KaiserSoft/OpenSimButtonBox/Cases and Enclosures/140mm wide/STL/Main Module - Face Plate - v4 - NO HOLES.STL

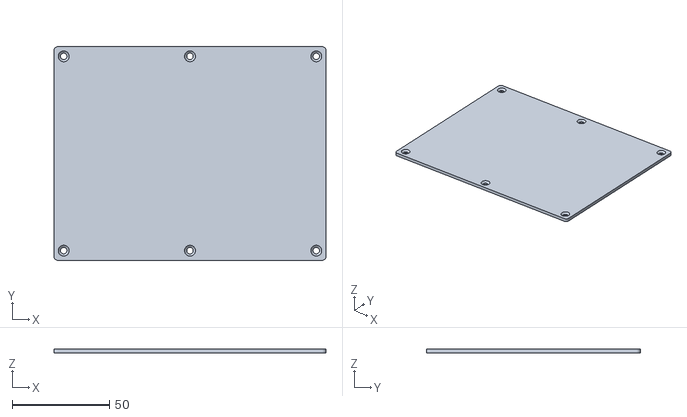
[picture p8: CAD file, 2016-06-05]
Cases and Enclosures/140mm wide/STL/Main Module - Face Plate - v4 - NO HOLES.STL
140.0 x 110.0 x 2.00
