KaiserSoft/OpenSimButtonBox/Cases and Enclosures/Mounting Bracket/Lowered Bracket/Mount Bracket 75 degrees.STL

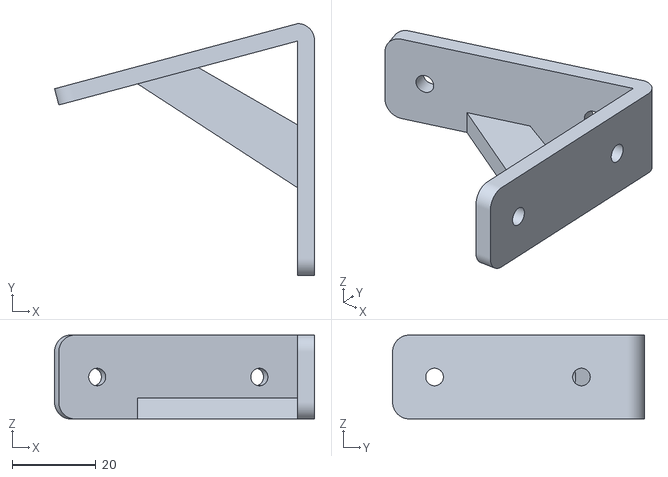
[picture p9: CAD file, 2016-05-30]
Cases and Enclosures/Mounting Bracket/Lowered Bracket/Mount Bracket 75 degrees.STL
62.0 x 60.0 x 20.0
