KaiserSoft/OpenSimButtonBox/Cases and Enclosures/Side Box Left/STL/Side Box Left - Face Plate v2 - TOP ROW PUSH BUTTONS.STL

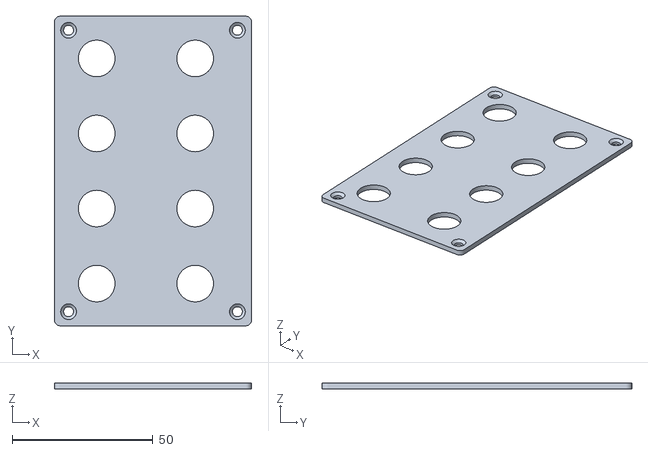
[picture p10: CAD file, 2016-12-20]
Cases and Enclosures/Side Box Left/STL/Side Box Left - Face Plate v2 - TOP ROW PUSH BUTTONS.STL
70.0 x 110.0 x 2.00
