KaiserSoft/OpenSimButtonBox/Magnetic Paddle Shifters/Box Style/Box Style - Body Top - RC1.STEP

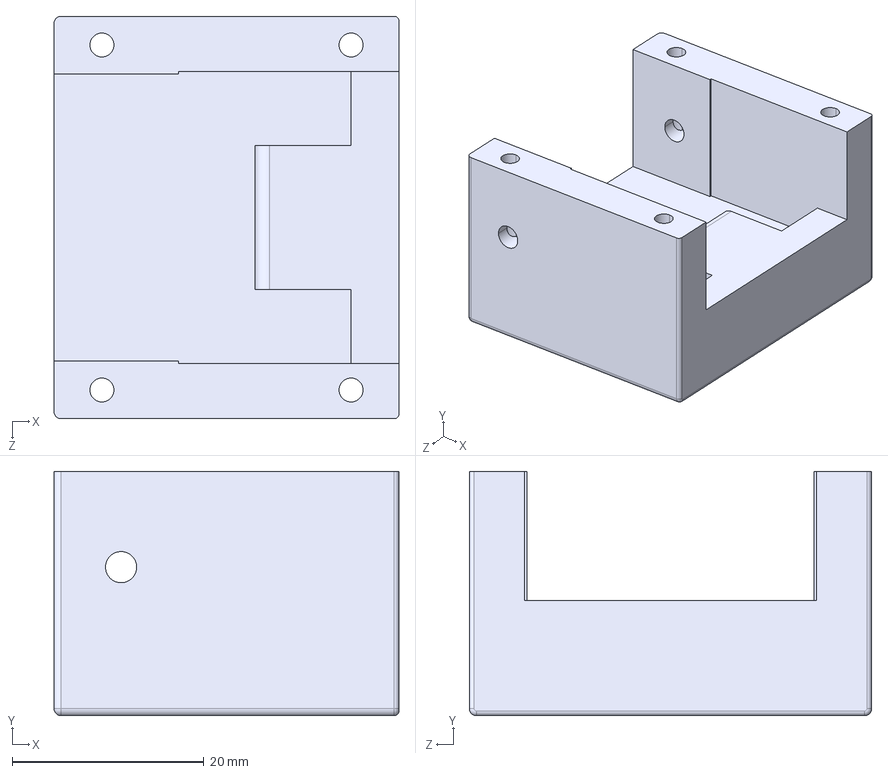
[picture p11: CAD file, 2017-08-28]
Magnetic Paddle Shifters/Box Style/Box Style - Body Top - RC1.STEP
36.0 x 25.5 x 42.0 mm
