KaiserSoft/OpenSimButtonBox/Wheel Button Box/Face Plate for 320mm Steering Wheel/Sparko - Momo - Spacer and Backplate - ProMicro.STEP

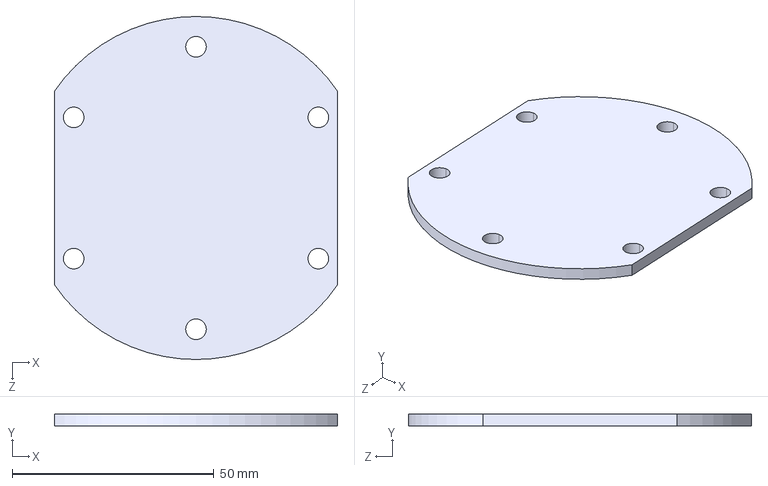
[picture p12: CAD file, 2017-09-29]
Wheel Button Box/Face Plate for 320mm Steering Wheel/Sparko - Momo - Spacer and Backplate - ProMicro.STEP
70.1 x 3.00 x 85.0 mm
