KaiserSoft/OpenSimButtonBox/Wheel Button Box/Face Plate for 320mm Steering Wheel/Wheel Box Face Plate for Arduino ProMicro - ONE PIECE.STL

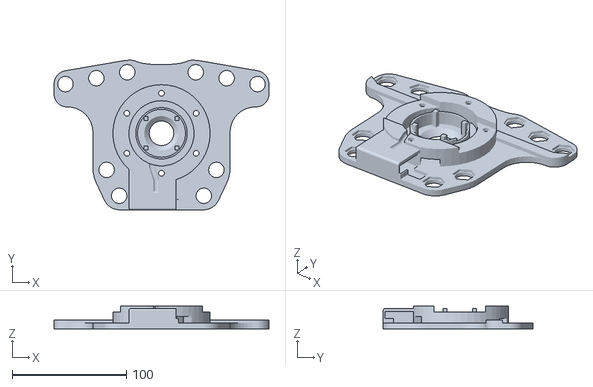
[picture p13: CAD file, 2017-09-29]
Wheel Button Box/Face Plate for 320mm Steering Wheel/Wheel Box Face Plate for Arduino ProMicro - ONE PIECE.STL
188.0 x 131.0 x 20.0
