KaiserSoft/OpenSimButtonBox/Magnetic Paddle Shifters/Box Style/Box Style - Lever - RC1.STEP

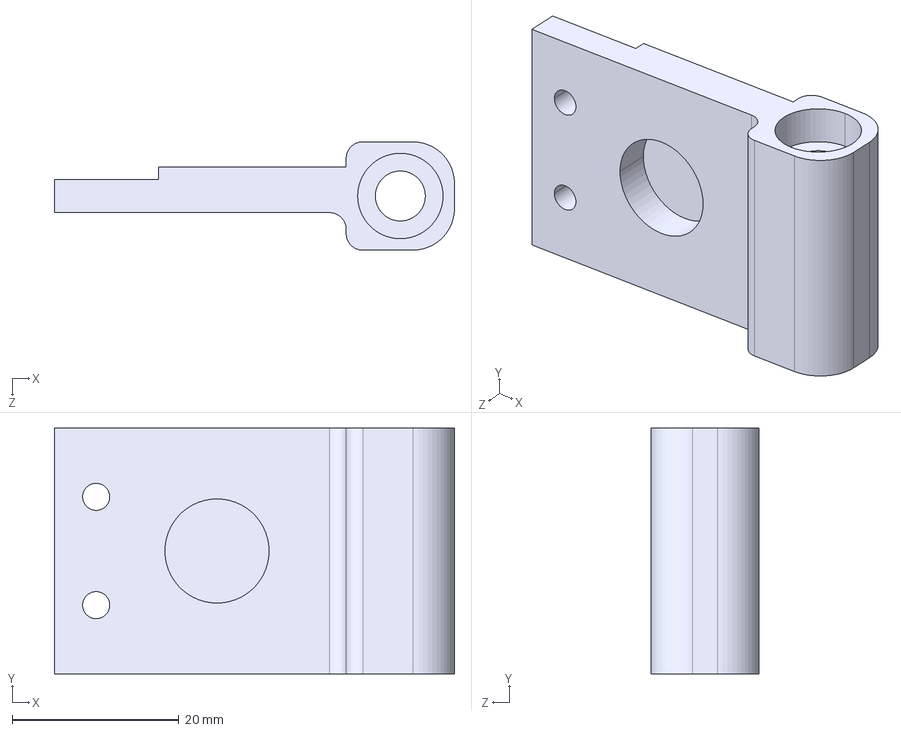
[picture p14: CAD file, 2017-08-28]
Magnetic Paddle Shifters/Box Style/Box Style - Lever - RC1.STEP
48.0 x 29.5 x 13.0 mm
