KaiserSoft/OpenSimButtonBox/Wheel Button Box/Face Plate for 320mm Steering Wheel/Wheel Box Face Plate for Arduino ProMicro - TWO PIECES - ONE.STL

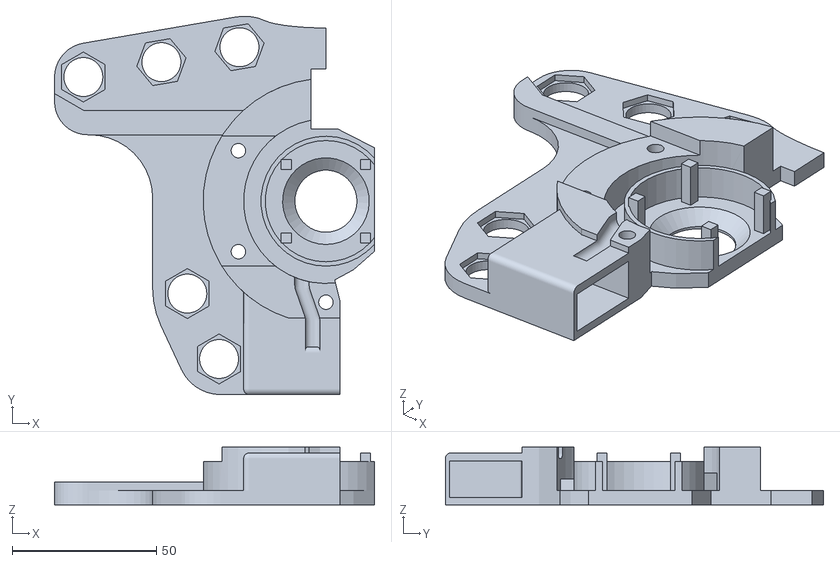
[picture p15: CAD file, 2017-09-29]
Wheel Button Box/Face Plate for 320mm Steering Wheel/Wheel Box Face Plate for Arduino ProMicro - TWO PIECES - ONE.STL
110.8 x 131.0 x 20.0
