KaiserSoft/OpenSimButtonBox/Cases and Enclosures/Encoder Knobs/Encoder Knob 1.3-HEX.STL

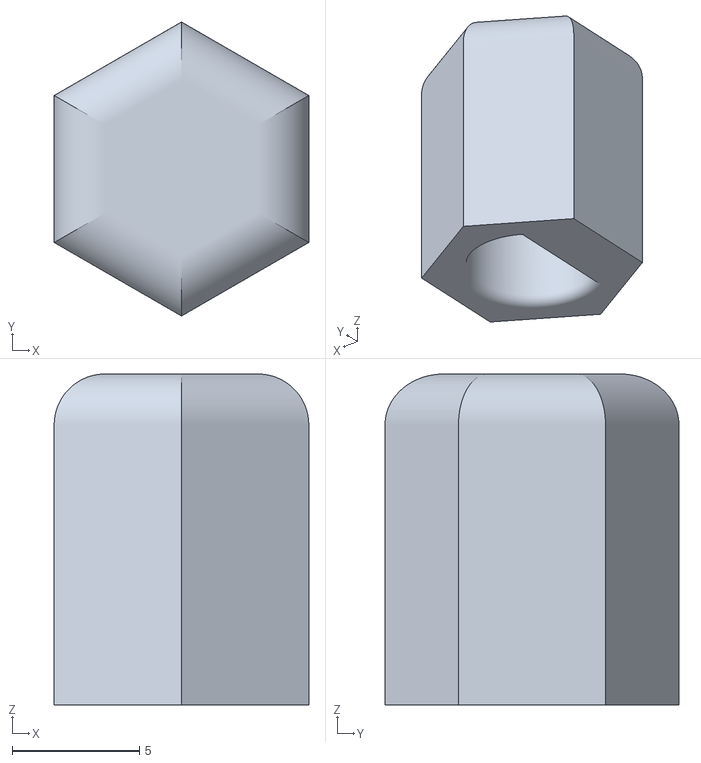
[picture p16: CAD file, 2016-06-12]
Cases and Enclosures/Encoder Knobs/Encoder Knob 1.3-HEX.STL
10.0 x 11.5 x 13.0
