KaiserSoft/OpenSimButtonBox/Cases and Enclosures/Side Box Left/STL/Side Box Left - Face Plate v2 - NO HOLES.STL

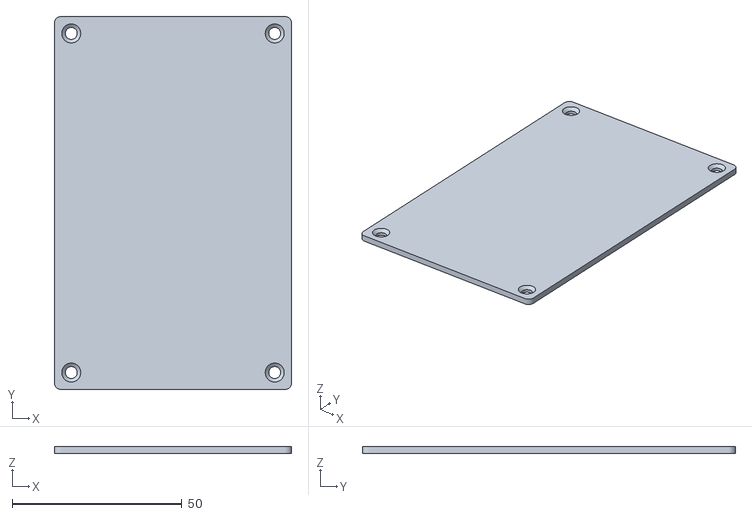
[picture p17: CAD file, 2016-06-05]
Cases and Enclosures/Side Box Left/STL/Side Box Left - Face Plate v2 - NO HOLES.STL
70.0 x 110.0 x 2.00
