KaiserSoft/OpenSimButtonBox/Wheel Button Box/Face Plate for 320mm Steering Wheel/Wheel Box Face Plate for Arduino ProMicro - TWO PIECES - TWO.STL

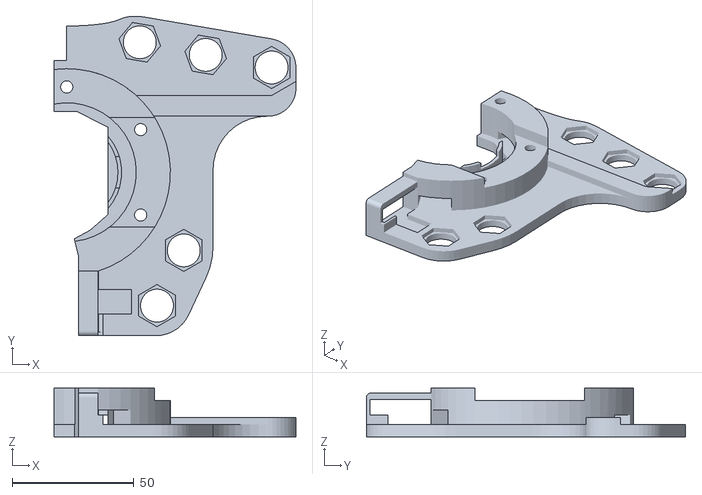
[picture p18: CAD file, 2017-09-29]
Wheel Button Box/Face Plate for 320mm Steering Wheel/Wheel Box Face Plate for Arduino ProMicro - TWO PIECES - TWO.STL
99.2 x 131.0 x 20.0
