KaiserSoft/OpenSimButtonBox/Magnetic Paddle Shifters/Box Style/Box Style - Body Bottom - RC1.STEP

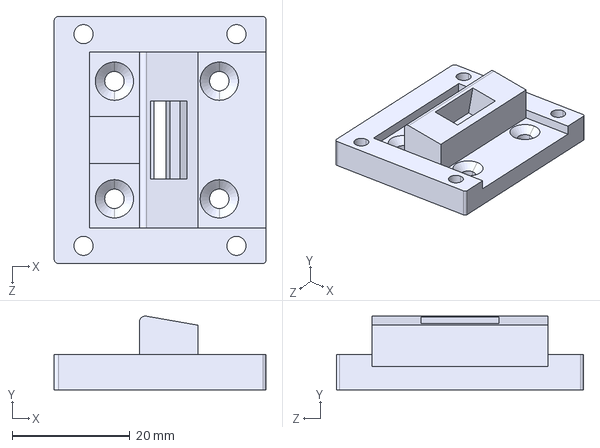
[picture p19: CAD file, 2017-08-28]
Magnetic Paddle Shifters/Box Style/Box Style - Body Bottom - RC1.STEP
36.0 x 12.6 x 42.0 mm
