KaiserSoft/OpenSimButtonBox/Wheel Button Box/Face Plate for 320mm Steering Wheel/Shifter Mount with Joystick Slot - v1b.STEP

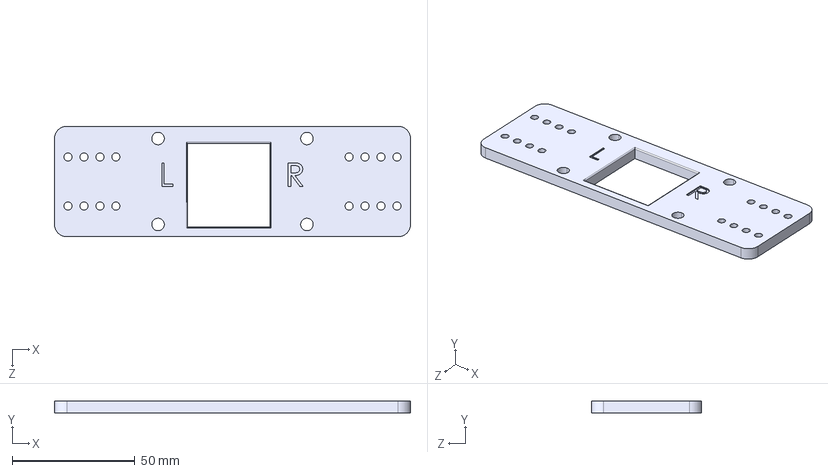
[picture p20: CAD file, 2017-09-29]
Wheel Button Box/Face Plate for 320mm Steering Wheel/Shifter Mount with Joystick Slot - v1b.STEP
145.0 x 5.00 x 45.0 mm
