KaiserSoft/OpenSimButtonBox/Mainboard/Code_MainModule/BUTTONS.h

/*
 ########################
 # Pit Limiter Settings #
 ########################
 
 * Setting "EnablePitLimiterSwitch" to 1 allows you to use a permanent (ON/OFF) switch
 * as a pit limiter. The pit limiter is activated when the switch is set to ON and turned
 * off again when the switch is set to OFF.
 * The value of "PitLimiterKey" is send once for "ON" and again for "OFF"
 */
#define EnablePitLimiterSwitch 1
#define PitLimiterPin 3     // pin for ON/OFF switch used as pit limiter
#define PitLimiterKey KEY_A // key for pit limiter. sent once when enabled and again when turned off
#define PitLimiterMod 0
#define PitLimiterHold 0
#define PitLimiterIgnoreOnAux 1 //ignore pit limter if any AUX key are set
                                // allows you turn the pit limiter off if you reset your car with it on.
                                // this may reset the car with the pit limiter off in car 
                                // but still on according to the button box


	


	
/*
 ###################
 # Shiter Priority #
 ###################

 * using this will check the multiplexer ports where your shifters are connected to after every port check
 * 
 * usually port 1 of every multiplexer is checked, then port 2 and so on
 * with shifter priority enabled, port 1 of every multi plexer is checked, then the shifter ports, then port 2 of every multi plexer, then the shifter ports again
 */
#define Enable_Shifter_Priority 0  // 1 to check for shifts more often then regular buttons, 0 to check during regular button checks
#define Shifter_A_Multiplexer 3    // multiplexer where the shifter is connected to - with DebugMultiplexer enabled, value "Device"
#define Shifter_A_Port 6           // port on multiplexer - with DebugMultiplexer enabled, value "MultiplexerPin"
#define Shifter_B_Multiplexer 3    // multiplexer where the shifter is connected to - with DebugMultiplexer enabled, value "Device"
#define Shifter_B_Port 2           // port on multiplexer - with DebugMultiplexer enabled, value "MultiplexerPin"
#define Shifter_Debounce 25        // time in ms that must pass before multiplexed buttons are considered pressed
 
 
								
								
								

								
								
/* 
  ###################
  # Rotary Encoders #
  ###################
*/
#define Encoder1PinA      7          // the pin the encoder is connected to
#define Encoder1ModA      MODIFIERKEY_SHIFT // modifier key to send
#define Encoder1KeyA      KEY_X      // key to send
#define Encoder1PinB      8         // the pin the encoder is connected to
#define Encoder1ModB      MODIFIERKEY_SHIFT // modifier key to send
#define Encoder1KeyB      KEY_Y      // key to send
#define Encoder1PinC      0          // encoder push button - not used when EnableMultiplexer is 1
#define Encoder1KeyC      0          // encoder push button - not used when EnableMultiplexer is 1
#define Encoder1ModC      0          // encoder push button - not used when EnableMultiplexer is 1
#define Encoder1HoldC     0          // encoder push button - not used when EnableMultiplexer is 1

#define Encoder2PinA      9         // the pin the encoder is connected to
#define Encoder2ModA      0          // modifier key to send
#define Encoder2KeyA      KEY_DOWN   // key to send
#define Encoder2PinB      10         // the pin the encoder is connected to
#define Encoder2ModB      0          // modifier key to send
#define Encoder2KeyB      KEY_UP     // key to send
#define Encoder2PinC      0          // encoder push button - not used when EnableMultiplexer is 1
#define Encoder2KeyC      0          // encoder push button - not used when EnableMultiplexer is 1
#define Encoder2ModC      0          // encoder push button - not used when EnableMultiplexer is 1
#define Encoder2HoldC     0          // encoder push button - not used when EnableMultiplexer is 1

#define Encoder3PinA      11         // the pin the encoder is connected to
#define Encoder3ModA      0          // modifier key to send
#define Encoder3KeyA      KEY_LEFT  // key to send
#define Encoder3PinB      12         // the pin the encoder is connected to
#define Encoder3ModB      0          // modifier key to send
#define Encoder3KeyB      KEY_RIGHT   // key to send
#define Encoder3PinC      0          // encoder push button - not used when EnableMultiplexer is 1
#define Encoder3KeyC      0          // encoder push button - not used when EnableMultiplexer is 1
#define Encoder3ModC      0          // encoder push button - not used when EnableMultiplexer is 1
#define Encoder3HoldC     0          // encoder push button - not used when EnableMultiplexer is 1







/* 
  #############################################
  # Buttons - multiplexed and non-multiplexed #
  #############################################
*/

//Pin 1
#define Button_5_Key KEY_A              // key to send
#define Button_5_Mod 0                  // modifier key to send
#define Button_5_Hold 0                 // 1 == send key until released, 0 == release after BUTTON_HOLD
#define Button_5_Pin 0                  // not used when EnableMultiplexer is 1

//Pin 2
#define Button_7_Key KEY_B              // key to send
#define Button_7_Mod 0                  // modifier key to send
#define Button_7_Hold 0                 // 1 == send key until released, 0 == release after BUTTON_HOLD
#define Button_7_Pin 0                  // not used when EnableMultiplexer is 1

//Pin 3
#define Button_8_Key KEY_C              // key to send
#define Button_8_Mod 0                  // modifier key to send
#define Button_8_Hold 0                 // 1 == send key until released, 0 == release after BUTTON_HOLD
#define Button_8_Pin 0                  // not used when EnableMultiplexer is 1

//Pin 4
#define Button_6_Key KEY_D              // key to send
#define Button_6_Mod 0                  // modifier key to send
#define Button_6_Hold 0                 // 1 == send key until released, 0 == release after BUTTON_HOLD
#define Button_6_Pin 0                  // not used when EnableMultiplexer is 1

//Pin 5
#define Button_3_Key KEY_SPACE              // key to send
//#define Button_3_Key KEY_E              // key to send
#define Button_3_Mod 0                  // modifier key to send
#define Button_3_Hold 0                 // 1 == send key until released, 0 == release after BUTTON_HOLD
#define Button_3_Pin 0                  // not used when EnableMultiplexer is 1

//Pin 6
#define Button_2_Key KEY_SPACE              // key to send
//#define Button_2_Key KEY_F              // key to send
#define Button_2_Mod 0                  // modifier key to send
#define Button_2_Hold 0                 // 1 == send key until released, 0 == release after BUTTON_HOLD
#define Button_2_Pin 0                  // not used when EnableMultiplexer is 1

//Pin 7
#define Button_1_Key KEY_F1              // key to send
//#define Button_1_Key KEY_G              // key to send
#define Button_1_Mod 0                  // modifier key to send
#define Button_1_Hold 0                 // 1 == send key until released, 0 == release after BUTTON_HOLD
#define Button_1_Pin 0                  // not used when EnableMultiplexer is 1

//Pin 8
#define Button_4_Key KEY_H              // key to send
#define Button_4_Mod 0                  // modifier key to send
#define Button_4_Hold 0                 // 1 == send key until released, 0 == release after BUTTON_HOLD
#define Button_4_Pin 0                  // not used when EnableMultiplexer is 1

//Pin 17
#define Button_13_Key KEY_Q             // key to send
#define Button_13_Mod 0                 // modifier key to send
#define Button_13_Hold 0                // 1 == send key until released, 0 == release after BUTTON_HOLD
#define Button_13_Pin 0                 // not used when EnableMultiplexer is 1

//Pin 18
#define Button_15_Key KEY_R             // key to send
#define Button_15_Mod 0                 // modifier key to send
#define Button_15_Hold 0                // 1 == send key until released, 0 == release after BUTTON_HOLD
#define Button_15_Pin 0                 // not used when EnableMultiplexer is 1

//Pin 23
#define Button_16_Key KEY_W             // key to send
#define Button_16_Mod 0                 // modifier key to send
#define Button_16_Hold 0                // 1 == send key until released, 0 == release after BUTTON_HOLD
#define Button_16_Pin 0                 // not used when EnableMultiplexer is 1

//Pin 24
//#define Button_14_Key KEY_X             // key to send
//#define Button_14_Mod 0                 // modifier key to send
//#define Button_14_Hold 0                // 1 == send key until released, 0 == release after BUTTON_HOLD
#define Button_14_Key KEY_R             // key to send
#define Button_14_Mod MODIFIERKEY_ALT                 // modifier key to send
#define Button_14_Hold 1                // 1 == send key until released, 0 == release after BUTTON_HOLD
#define Button_14_Pin 0                 // not used when EnableMultiplexer is 1

//Pin 19
#define Button_11_Key KEY_S             // key to send
#define Button_11_Mod 0                 // modifier key to send
#define Button_11_Hold 0                // 1 == send key until released, 0 == release after BUTTON_HOLD
#define Button_11_Pin 0                 // not used when EnableMultiplexer is 1

//Pin 20
#define Button_10_Key KEY_T             // key to send
#define Button_10_Mod 0                 // modifier key to send
#define Button_10_Hold 0                // 1 == send key until released, 0 == release after BUTTON_HOLD
#define Button_10_Pin 0                 // not used when EnableMultiplexer is 1

//Pin 21
#define Button_9_Key KEY_U              // key to send
#define Button_9_Mod 0                  // modifier key to send
#define Button_9_Hold 0                 // 1 == send key until released, 0 == release after BUTTON_HOLD
#define Button_9_Pin 0                  // not used when EnableMultiplexer is 1

//Pin 22
#define Button_12_Key KEY_V             // key to send
#define Button_12_Mod 0                 // modifier key to send
#define Button_12_Hold 0                // 1 == send key until released, 0 == release after BUTTON_HOLD
#define Button_12_Pin 0                 // not used when EnableMultiplexer is 1



/* 
  ##############################
  # Buttons - multiplexed ONLY #
  ##############################
*/
//Pin 9
#define Button_21_Key KEY_I             // key to send
#define Button_21_Mod 0                 // modifier key to send
#define Button_21_Hold 0                // 1 == send key until released, 0 == release after BUTTON_HOLD

//Pin 10
#define Button_23_Key KEY_J             // key to send
#define Button_23_Mod 0                 // modifier key to send
#define Button_23_Hold 0                // 1 == send key until released, 0 == release after BUTTON_HOLD

//Pin 15
#define Button_24_Key KEY_O             // key to send
#define Button_24_Mod 0                 // modifier key to send
#define Button_24_Hold 0                // 1 == send key until released, 0 == release after BUTTON_HOLD

//Pin 16
#define Button_22_Key KEY_P            // key to send
#define Button_22_Mod 0                 // modifier key to send
#define Button_22_Hold 0                // 1 == send key until released, 0 == release after BUTTON_HOLD

//Pin 11
#define Button_19_Key KEY_K            // key to send
#define Button_19_Mod 0                 // modifier key to send
#define Button_19_Hold 0                // 1 == send key until released, 0 == release after BUTTON_HOLD

//Pin 12
#define Button_18_Key KEY_L             // key to send
#define Button_18_Mod 0                 // modifier key to send
#define Button_18_Hold 0                // 1 == send key until released, 0 == release after BUTTON_HOLD

//Pin 13
#define Button_17_Key KEY_M             // key to send
#define Button_17_Mod 0                 // modifier key to send
#define Button_17_Hold 0                // 1 == send key until released, 0 == release after BUTTON_HOLD

//Pin 14
#define Button_20_Key KEY_N             // key to send
#define Button_20_Mod 0                 // modifier key to send
#define Button_20_Hold 0                // 1 == send key until released, 0 == release after BUTTON_HOLD

//Pin 28
#define Button_32_Key KEY_D             // key to send
#define Button_32_Mod MODIFIERKEY_SHIFT // modifier key to send
#define Button_32_Hold 0                // 1 == send key until released, 0 == release after BUTTON_HOLD

//Pin 25
#define Button_30_Key KEY_A             // key to send
#define Button_30_Mod MODIFIERKEY_SHIFT // modifier key to send
#define Button_30_Hold 0                // 1 == send key until released, 0 == release after BUTTON_HOLD

//Pin 31
#define Button_31_Key KEY_G             // key to send
#define Button_31_Mod MODIFIERKEY_SHIFT // modifier key to send
#define Button_31_Hold 0                // 1 == send key until released, 0 == release after BUTTON_HOLD

//Pin 30
#define Button_29_Key KEY_F             // key to send
#define Button_29_Mod MODIFIERKEY_SHIFT // modifier key to send
#define Button_29_Hold 0                // 1 == send key until released, 0 == release after BUTTON_HOLD

//Pin 26
#define Button_28_Key KEY_B             // key to send
#define Button_28_Mod MODIFIERKEY_SHIFT // modifier key to send
#define Button_28_Hold 0                // 1 == send key until released, 0 == release after BUTTON_HOLD

//Pin 27
#define Button_25_Key KEY_C             // key to send
#define Button_25_Mod MODIFIERKEY_SHIFT // modifier key to send
#define Button_25_Hold 0                // 1 == send key until released, 0 == release after BUTTON_HOLD

//Pin 29
//#define Button_26_Key KEY_E            // key to send
//#define Button_26_Mod MODIFIERKEY_SHIFT // modifier key to send
//#define Button_26_Hold 0                // 1 == send key until released, 0 == release after BUTTON_HOLD
#define Button_26_Key KEY_ESC            // key to send
#define Button_26_Mod 0 // modifier key to send
#define Button_26_Hold 1                // 1 == send key until released, 0 == release after BUTTON_HOLD

//Pin 32
#define Button_27_Key KEY_H             // key to send
#define Button_27_Mod MODIFIERKEY_SHIFT // modifier key to send
#define Button_27_Hold 0                // 1 == send key until released, 0 == release after BUTTON_HOLD
